Chris-Johnston/crobagotchi/crobagotchi/sprites.cpp

#include "sprites.h"

// https://javl.github.io/image2cpp/

const unsigned char epd_bitmap_fry [] PROGMEM = {
	0x00, 0x00, 0x00, 0x60, 0xc0, 0x80, 0xc0, 0x00, 0xc0, 0xe0, 0x40, 0x80, 0x00, 0xe0, 0x00, 0xc0, 
	0x00, 0xe0, 0x80, 0xc0, 0x60, 0x00, 0x00, 0x00, 0x00, 0x00, 0x00, 0x00, 0x1e, 0xe3, 0x03, 0xf3, 
	0x57, 0x07, 0xf6, 0x56, 0xa7, 0x14, 0xe7, 0x14, 0x02, 0xf3, 0x0f, 0x00, 0x00, 0x00, 0x00, 0x00, 
	0x00, 0x00, 0x00, 0x00, 0x00, 0x03, 0x3c, 0x20, 0x20, 0x20, 0x10, 0x10, 0x10, 0x10, 0x20, 0x20, 
	0x3c, 0x03, 0x00, 0x00, 0x00, 0x00, 0x00, 0x00
};

// 'leg dithered', 128x64px
// const unsigned char epd_bitmap_leg_dithered [] PROGMEM = {
//   0x00, 0x00, 0x00, 0x00, 0x00, 0x00, 0x00, 0x00, 0x00, 0x00, 0x00, 0x00, 0x00, 0x00, 0x00, 0x00, 
//   0x00, 0x00, 0x00, 0x00, 0x00, 0x00, 0x00, 0x00, 0x00, 0x00, 0x00, 0x00, 0x00, 0x00, 0x00, 0x00, 
//   0x00, 0x00, 0x00, 0x00, 0x00, 0x00, 0x00, 0x00, 0x00, 0x00, 0x00, 0x00, 0x40, 0x80, 0x78, 0x80, 
//   0x2c, 0xd0, 0x2c, 0xd0, 0x24, 0xc8, 0xd0, 0xa0, 0xc0, 0xc0, 0x80, 0x80, 0x80, 0x80, 0x80, 0x80, 
//   0x80, 0x80, 0xc0, 0x00, 0x80, 0x80, 0x00, 0x00, 0x00, 0x00, 0x00, 0x00, 0x00, 0x00, 0x00, 0x00, 
//   0x00, 0x00, 0x00, 0x00, 0x00, 0x00, 0x00, 0x00, 0x00, 0x00, 0x00, 0x00, 0x00, 0x00, 0x00, 0x00, 
//   0x00, 0x00, 0x00, 0x00, 0x00, 0x00, 0x00, 0x00, 0x00, 0x00, 0x00, 0x00, 0x00, 0x00, 0x00, 0x00, 
//   0x00, 0x00, 0x00, 0x00, 0x00, 0x00, 0x00, 0x00, 0x00, 0x00, 0x00, 0x00, 0x00, 0x00, 0x00, 0x00, 
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
// 	0x00, 0x00, 0x00, 0x0c, 0x02, 0x0d, 0x03, 0x07, 0x01, 0x02, 0x00, 0x0a, 0x00, 0x05, 0x0a, 0x00, 
// 	0x01, 0x00, 0x02, 0x00, 0x04, 0x00, 0x00, 0x02, 0x08, 0x02, 0x01, 0x00, 0x00, 0x00, 0x08, 0x07
// };
